bastoon577-lang/Module_TIC/SOFTWARE/Module_TIC/src/ihm_exploitation_page.h

const char* htmlPageExploit PROGMEM = R"rawliteral(
  <div class="hamburger" onclick="toggleMenu()">
    <div></div>
    <div></div>
    <div></div>
  </div>
  <div class="nav-menu" id="menu">
    <a onclick="activerContainer(1)">Données TIC</a>
	<a onclick="activerContainer(2)">Filtre de données</a>
    <a onclick="activerContainer(3)">Configurations système</a>
    <a onclick="activerContainer(4)">À propos</a>
  </div>
  
  <div id="container1" class="container">
    <h1>Données TIC</h1>
    <div id="tab1"></div>
  </div>
  
  <div id="container2" class="container">
    <h1>Filtre de données</h1>
	<div class="filter-box">
      <input type="text" id="filtr" placeholder="IINST,ISOUSC,EAST">
      <button class="button" id="filtr-submit">Soumettre</button>
      <button class="button" id="filtr-reset">Réinitialiser</button>
	</div>
  </div>

  <div id="container3" class="container">
    <h1>Système</h1>
    <button class="button" onclick="handleRequest('theme',function(){toggleTheme();})">Basculer le Thème</button>
    <button class="button warning" onclick="handleReset();">Retour Usine</button>
    <h2>Générale</h2>
    <div id="tab2"></div>
  </div>

  <div id="container4" class="container">
    <h1>A propos</h1>
    <p>Dispositif de visualisation des données Linky issues du bornier TIC sur un réseau Wi-Fi. Compatible sur les compteurs 
    Linky monophasés et triphasés, ce dispositif permet:</p>
    <p>L'affichage des données dans l'onglet <b>Données Linky</b></p>
    <p>D'offrir les données au travers d'un service <b>WebSocket</b></p>
  </div>

  <div id="container10" class="container">
    <h1>Redémarrage</h1>
    <p>La configuration à été prise en compte, votre équipement à redémarré</p>
    <p class="alert">La connexion avec le ModuleTIC est perdue, veuillez vous reconnecter</p>
  </div>
)rawliteral";

const char* scriptsPageExploit PROGMEM = R"rawliteral(
  function refresh(idContainer) {
    location.hash = idContainer;
    location.reload();
  }

  function handleReset() {
    if (showPopupConfirm('Votre équipement va être réinitialisé, ce qui implique une reconfiguration de celui-ci, souhaitez-vous continuer ?')) {
      handleRequest('reset',function(){next(10);})
    }
    return false;
  }

  function showPopupConfirm(msg) {
    return confirm(msg);
  }

  function toggleMenu() {
    const menu = document.getElementById('menu');
    menu.classList.toggle('open');
  }
  
  document.addEventListener('click', function(event) {
    const menu = document.getElementById('menu');
    const hamburger = document.querySelector('.hamburger');
    if (hamburger.contains(event.target)) {
        return;
    }
    if (!menu.contains(event.target)) {
        menu.classList.remove('open');
    }
    const menuItems = menu.querySelectorAll('a, button');
    menuItems.forEach(item => {
        if (item.contains(event.target)) {
            menu.classList.remove('open');
        }
    });
  });

  function createTable(tabId) {
    const tableContainer = document.getElementById(tabId);
    const table = document.createElement('table');
    table.style.width = '100%';
    table.style.borderCollapse = 'collapse';
    const thead = document.createElement('thead');
    const headerRow = document.createElement('tr');
    const headerCell1 = document.createElement('th');
    headerCell1.textContent = "Description";
    const headerCell2 = document.createElement('th');
    headerCell2.textContent = "Valeur";
    headerRow.appendChild(headerCell1);
    headerRow.appendChild(headerCell2);
    thead.appendChild(headerRow);
    const tbody = document.createElement('tbody');
    table.appendChild(thead);
    table.appendChild(tbody);
    tableContainer.appendChild(table);
  }

  function addTableLinkyData(tabId,description,value) {
    const tableContainer = document.getElementById(tabId);
    const table = tableContainer.querySelector('table');
    const tbody = table.querySelector('tbody');
    const row = document.createElement('tr');
    const descriptionCell = document.createElement('td');
    descriptionCell.textContent = description;
    const valueCell = document.createElement('td');
    valueCell.id = description;
    valueCell.textContent = value;
    row.appendChild(descriptionCell);
    row.appendChild(valueCell);
    tbody.appendChild(row);
  }

  function addTableRow(tabId,description,value) {
    const tableContainer = document.getElementById(tabId);
    const table = tableContainer.querySelector('table');
    const tbody = table.querySelector('tbody');
    const row = document.createElement('tr');
    const descriptionCell = document.createElement('td');
    descriptionCell.textContent = description;
    const valueCell = document.createElement('td');
    valueCell.textContent = value;
    row.appendChild(descriptionCell);
    row.appendChild(valueCell);
    tbody.appendChild(row);
  }

  function updateButton(id, options = {}) {
    const btn = document.getElementById(id);
    if ('hidden' in options)
      btn.style.display = options.hidden ? 'none' : '';
    if ('warning' in options)
      btn.classList.toggle('warning', options.warning);
    if ('disabled' in options)
      btn.disabled = options.disabled;
  }
  
  function toggleButton(button) {
    if (button.classList.contains('warning')) {
      button.classList.remove('warning');
    } else {
      button.classList.add('warning');
    }
  }
  
  function updateTableDisplay(containerId, cleanString) {
    const container = document.getElementById(containerId);
    if (!container) return;

    const inputElement = document.getElementById("filtr");

    let formattedString = "";
    if (cleanString) {
      formattedString = String(cleanString)
        .split(",")
        .map(term => term.replace(/\s+/g, "").toUpperCase())
        .filter(term => term.length > 0)
        .join(",");
    }

    if (inputElement) {
      inputElement.value = formattedString;
    }

    const parent = container.querySelector("tbody") || container.querySelector("table") || container;
    const rows = Array.from(container.querySelectorAll("tr"));
    const dataRows = rows.filter(row => !row.querySelector("th") && row.querySelectorAll("td").length > 0);
    const targets = formattedString ? formattedString.split(",") : [];

    if (targets.length === 0) {
      dataRows.forEach(row => {
        row.style.display = "";
      });
    } else {
      dataRows.forEach(row => {
        row.style.display = "none";
      });

      targets.forEach(target => {
        dataRows.forEach(row => {
          const cell = row.querySelectorAll("td")[0];
          if (!cell) return;

          const label = cell.textContent.trim().toUpperCase();

          if (label.includes(target)) {
            row.style.display = "";
            parent.appendChild(row); // Déplace la ligne à la suite dans l'ordre du filtre
          }
        });
      });
    }
  }

  function filterTable(filterString) {
    const inputElement = document.getElementById("filtr");
    const valueToSend = filterString !== undefined ? filterString : (inputElement ? inputElement.value : "");

    let cleanString = "";
    if (valueToSend) {
      cleanString = String(valueToSend)
        .split(",")
        .map(term => term.replace(/\s+/g, "").toUpperCase())
        .filter(term => term.length > 0)
        .join(",");
    }

    if (cleanString.length > 128) {
      alert("Le filtre est trop long (supérieur à 128 caractères)");
      return;
    }

    const postData = "filtr=" + encodeURIComponent(cleanString);

    handleComplexRequest("filtr", postData, function() {
      updateTableDisplay("tab1", cleanString);
      next(1);
    });
  }

  document.getElementById("filtr-submit")?.addEventListener("click", function() {
    filterTable();
  });

  document.getElementById("filtr-reset")?.addEventListener("click", function() {
    filterTable("");
  });

  window.onload = function() {
    const hash = window.location.hash;
    if (hash) {
      activerContainer(hash.substring(1));
    } else {
      activerContainer(1);
    }
)rawliteral";

const char* scriptsPageExploitExtend PROGMEM = R"rawliteral(
  function initWebSocket(portWS) {
    ws = new WebSocket('ws://' + window.location.hostname + ':' + portWS + '/');
    ws.onmessage = function(event) {
      try {
        var data = JSON.parse(event.data);
        for (var key in data) {
          var value = data[key];
          var element = document.getElementById(key);
          if(element) {
            element.textContent = value;
          }
        }
      } catch (error) {
        console.error("Erreur:", error,event.data);
      }
    };
  }
)rawliteral";
