bastoon577-lang/Module_TIC/SOFTWARE/Module_TIC/eeprom_utils.cpp

#include <EEPROM.h>

#include "eeprom_utils.h"

/**
 * \fn void eeprom_init(void)
 */
void eeprom_init(void) {
  EEPROM.begin(EEPROM_SIZE);
}

/**
 * \fn void eeprom_write_data(void* data, EepromDataType type)
 */
void eeprom_write_data(void* data, EepromDataType type) {
  switch (type) {
    case EEPROM_STATIC_CFG:
      EEPROM.put(BASE_ADDR_STATIC_CFG, *(STATIC_CONF_FIELDS_t*)data);
      break;

    case EEPROM_VOLATILE_CFG:
      EEPROM.put(BASE_ADDR_VOLATILE_CFG, *(VOLATILE_CONF_FIELDS_t*)data);
      break;

    default:
      return;
  }
  EEPROM.commit();
}

/**
 * \fn void eeprom_read_data(void* data, EepromDataType type)
 */
void eeprom_read_data(void* data, EepromDataType type) {
  switch (type) {

    case EEPROM_STATIC_CFG:
      EEPROM.get(BASE_ADDR_STATIC_CFG, *(STATIC_CONF_FIELDS_t*)data);
      break;

    case EEPROM_VOLATILE_CFG:
      EEPROM.get(BASE_ADDR_VOLATILE_CFG, *(VOLATILE_CONF_FIELDS_t*)data);
      break;

    default :
      return;
  }
}
